iurretame32D/CO2-out/4.taldea/3D Kutxa/Erabilitako Linkak/linkak.odt

DHT_11

https://randomnerdtutorials.com/esp32-dht11-dht22-temperature-humidity-sensor-arduino-ide/

HEAT INDEX (sentsazio termikoa)

The heat index is a parameter that takes into account temperature and relative humidity, to determine the apparent temperature or the human perceived equivalent temperature.

Liburutegia eta kontrol aukerak

https://github.com/mysensors/MySensorsArduinoExamples/pull/35/files

CCS811

https://www.luisllamas.es/medir-calidad-del-aire-y-co2-con-ccs811-y-arduino/

LoRa

https://www.iagua.es/blogs/carles-bianciotto/conectar-sensor-lorawan-cero

https://bricolabs.cc/wiki/guias/lora_ttn

PINOUT erabilita daudenak eta liburutegiak

https://randomnerdtutorials.com/ttgo-lora32-sx1276-arduino-ide/

IKUSTEKO TTN pausuak

https://akirasan.net/nodo-lorawan-con-esp32/
