iurretame32D/CO2-out/Ataldea/Txostena/ZATIKA/Bloke_Diagrama.odt

# Bloke-diagramak

Lehen bertsioa izango da hau. Erronkaren amaieran igo egingo duzue azken bertsioa.

## Softwarearen hasierako bloke-diagrama

Softwarea: geziekin, bloke bakoitza zelan eta zertarako erabiliko den azalduta azpian. Aldagaiak eta funtzioen izenak aurreikustea ere komeniko litzateke. Sekuentzia edo ordena inportantea dela kontutan izan.

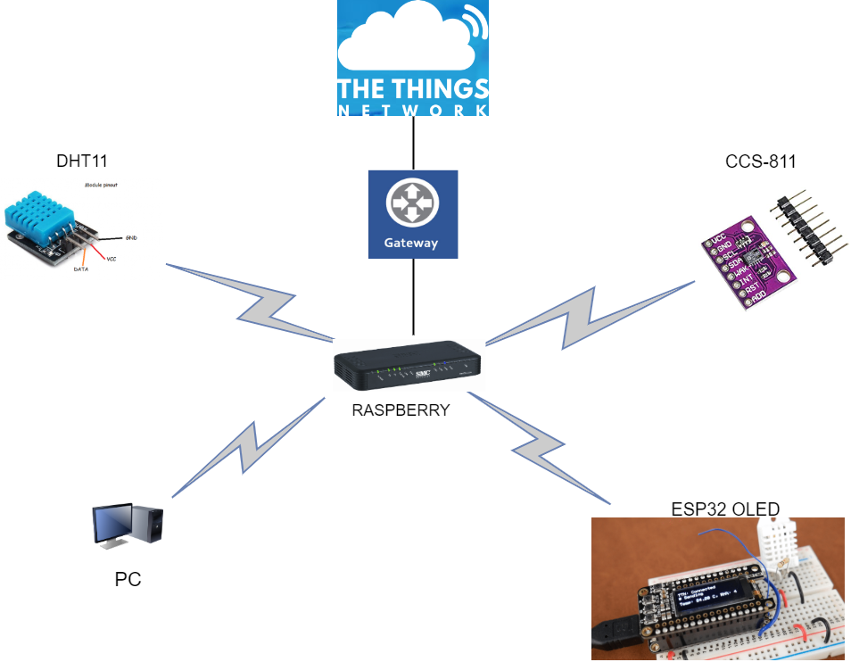
[picture p149: figure]

## Hardwarearen hasierako bloke-diagram

Hardwarea: geziekin, bloke bakoitza zelan eta zertarako erabiliko den azalduta azpian.

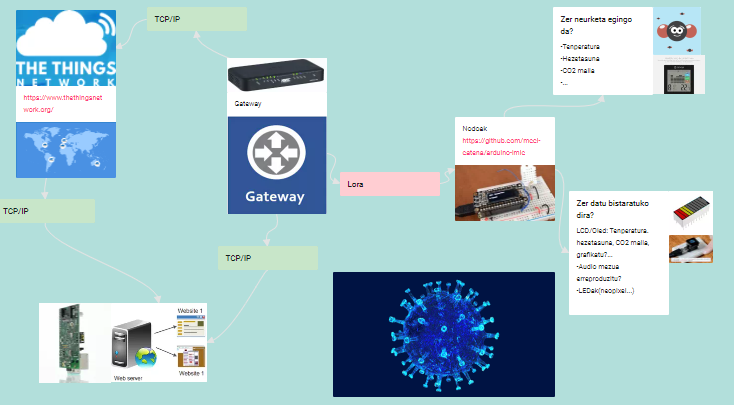
[picture p150: figure]

## Softwarearen amaierako bloke-diagrama

Softwarea: geziekin, bloke bakoitza zelan eta zertarako erabiliko den azalduta azpian. Aldagaiak eta funtzioen izenak aurreikustea ere komeniko litzateke. Sekuentzia edo ordena inportantea dela kontutan izan.

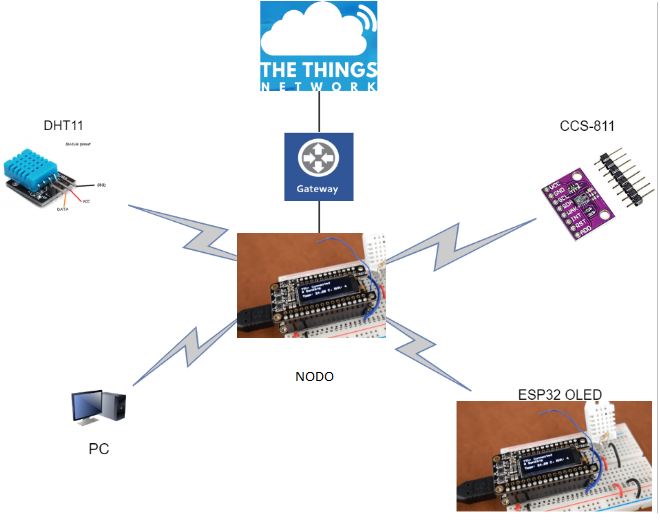
[picture p151: figure]

## Hardwarearen amaierako bloke-diagrama

Hardwarea: geziekin, bloke bakoitza zelan eta zertarako erabiliko den azalduta azpian.

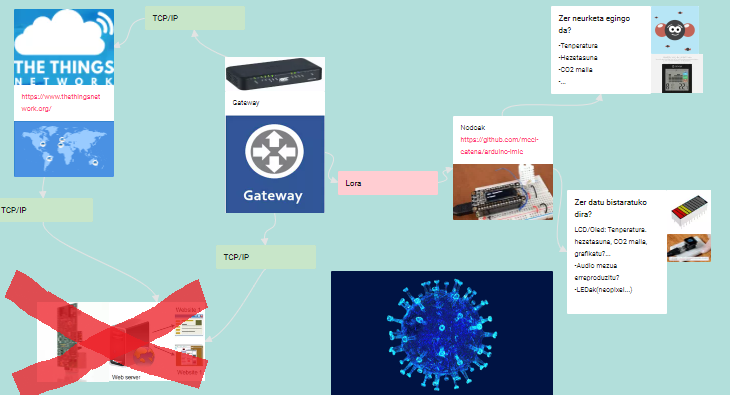
[picture p152: figure]
