iurretame32D/CO2-out/Talde3AnderBJonS/Txostenak/Atalak/BlokeDiagramak.odt

# Bloke-diagramak

## Softwarearen hasierako bloke-diagrama

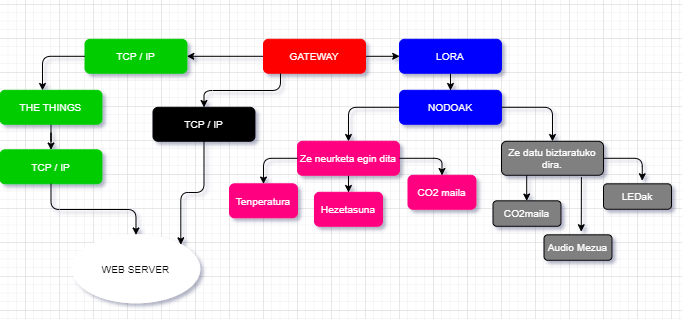
[picture p153: figure]

## Hardwarearen hasierako bloke-diagrama

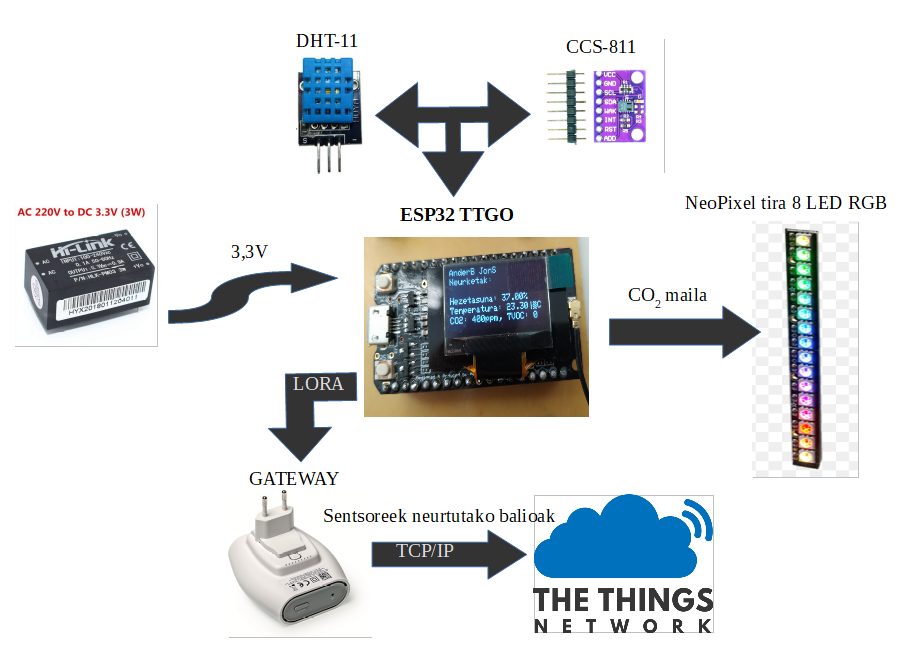
[picture p154: figure]
