iurretame32D/CO2-out/Talde3AnderBJonS/Txostenak/Atalak/ErronkarenPlanteamendua.odt

# Erronkaren planteamendua

Erronka honetan bi sentsore erabiliko ditugu, DHT-11 hezetasun eta tenperatura sentsorea eta CJMU-811 edo CCS-811 aireko CO2 kantitatea eta TVOC (bolatil konposatu organikoak) neurtze duena.

ESP32 TTGO kontrolagailuarekin lan egingo dugu, eta LORA komunikazioa erabiliko dugu, gure kontrolagailua, konfiguratu dugun GateWay-arekin komunikatzeko eta balioak partekatu ahal izateko.

Ondoren GateWay-a konfiguratu dugu TTN (The things Network)ean sortu dugun kontu batean sentsoreetako balioak bertan bistaratzeko.

Eta azkenik Raspberry bat erabiliz dashboard edo aginte panel bat sortzeko eta hor partekatzeko gure ditugun balioak edo informazioa.

Gure helburua elektronika eraikinaren geletako CO2 kantiatea, tenperatura eta hezetasunaren kontrola izatea da, eta edozein lekutan egonda, balio hauek ikus ahal izatea.

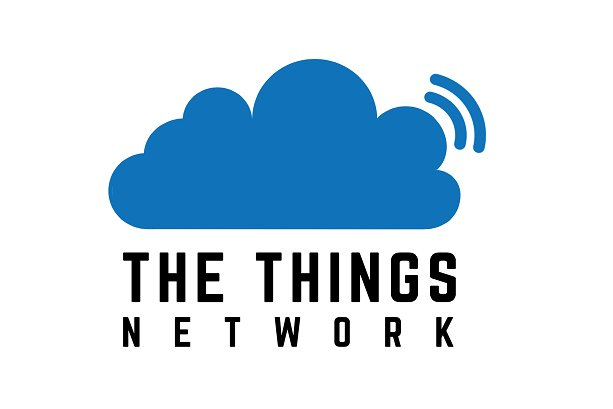
[picture p155: figure]
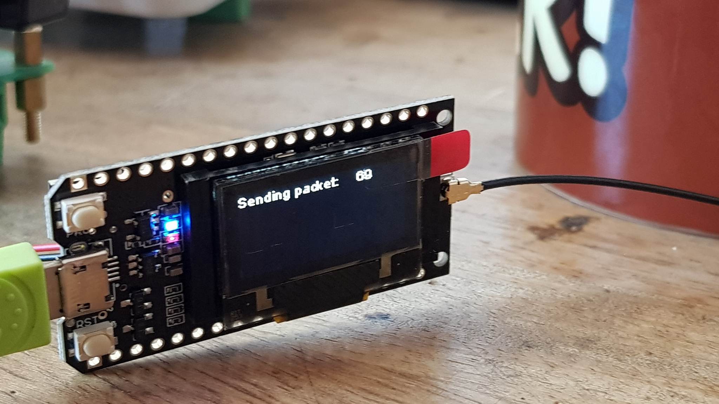
[picture p156: figure]
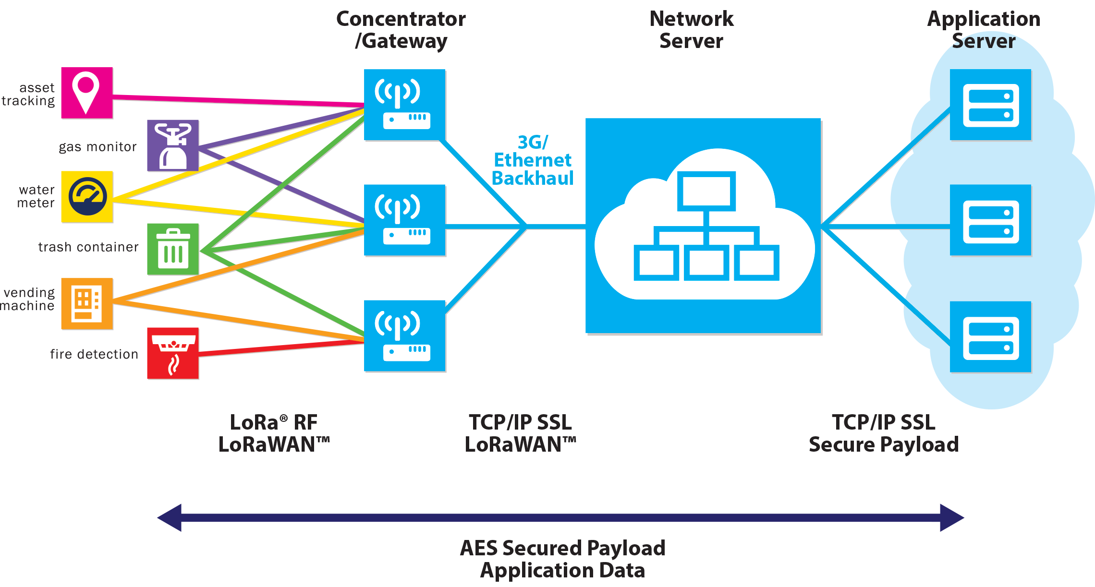
[picture p157: figure]
