iurretame32D/CO2-out/Talde3AnderBJonS/FRITZING/ccs811-arduino-1200x690.jpg

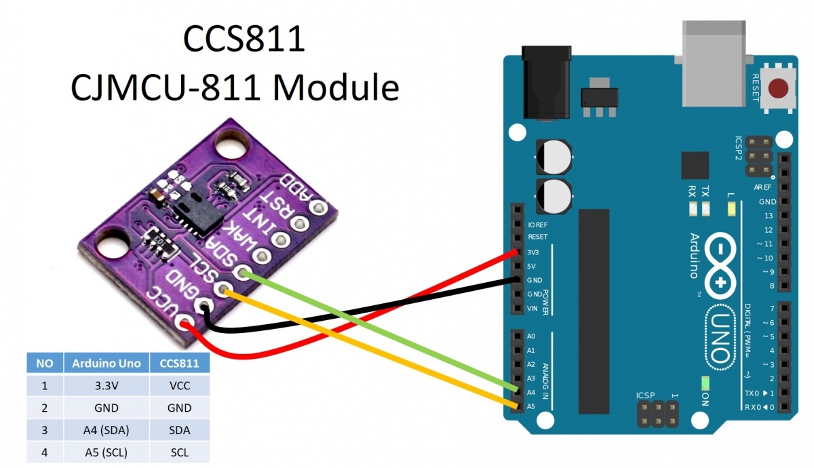
Talde3AnderBJonS/FRITZING/ccs811-arduino-1200x690.jpg
