iurretame32D/CO2-out/Talde3AnderBJonS/FRITZING/CCS811/CCS811_bb.png

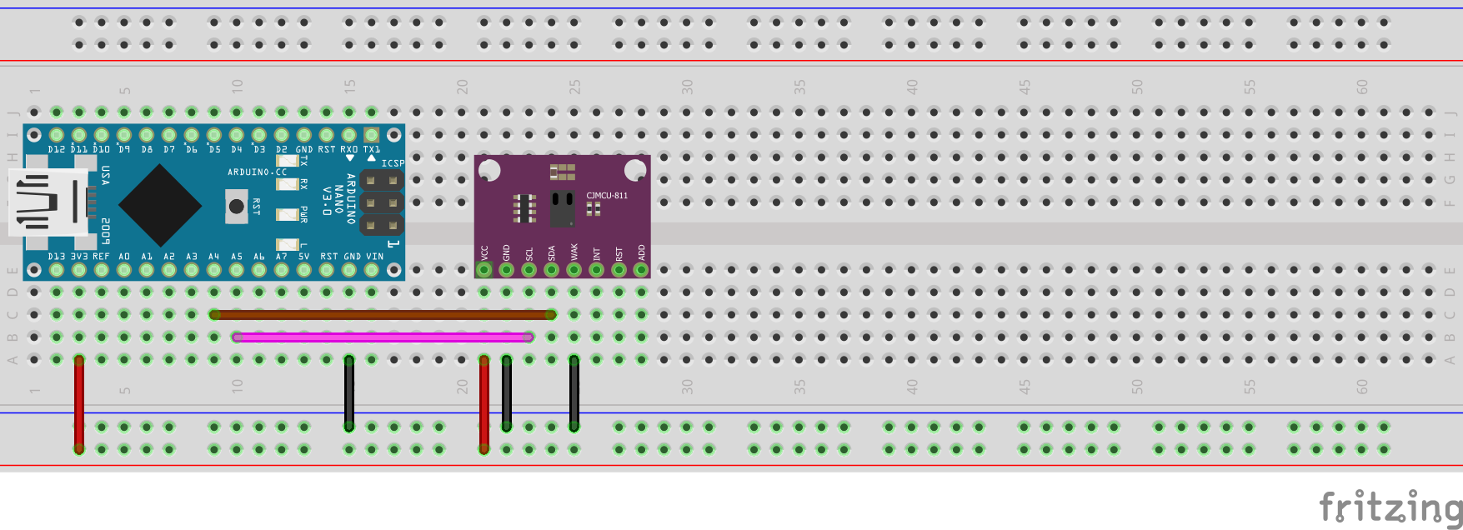
Talde3AnderBJonS/FRITZING/CCS811/CCS811_bb.png
