iurretame32D/CO2-out/Talde3AnderBJonS/FRITZING/cjmcu-811.png

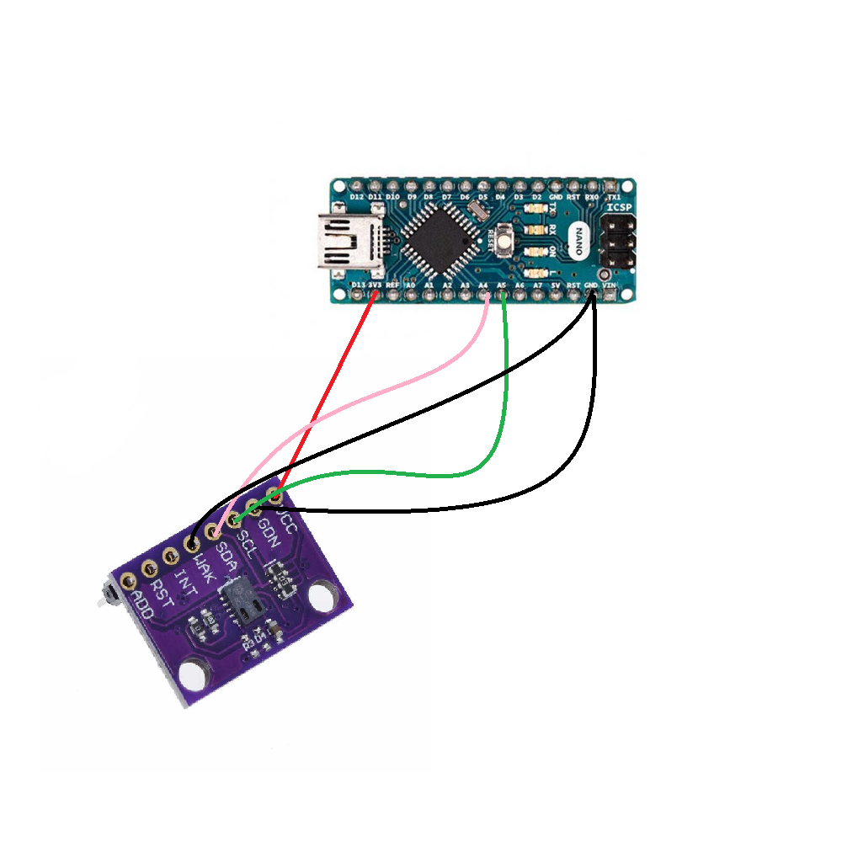
Talde3AnderBJonS/FRITZING/cjmcu-811.png
