iurretame32D/CO2-out/Talde3AnderBJonS/FRITZING/DHT11/DHT11.PNG

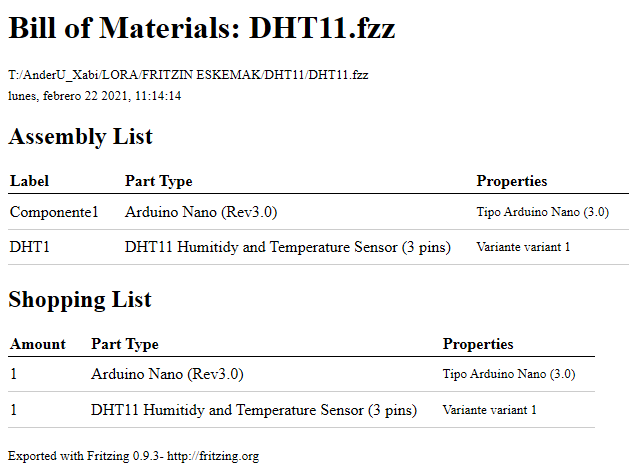
Talde3AnderBJonS/FRITZING/DHT11/DHT11.PNG
