iurretame32D/CO2-out/2.taldea/Proiektu Finala 2.Taldea/Arduino Programa/TTN_komunikazioa_proba/TTN_komunikazioa_proba.ino

#include <TheThingsNetwork.h>

// First install "DHT sensor library" via the Library Manager
#include <DHT.h>

// Set your AppEUI and AppKey
const char *appEui = "0000000000000000";
const char *appKey = "00000000000000000000000000000000";

#define loraSerial Serial1
#define debugSerial Serial

// Replace REPLACE_ME with TTN_FP_EU868 or TTN_FP_US915
#define freqPlan TTN_FP_EU868

#define DHTPIN 17

//Choose your DHT sensor moddel
#define DHTTYPE DHT11
//#define DHTTYPE DHT21
//#define DHTTYPE DHT22

DHT dht(DHTPIN, DHTTYPE);

TheThingsNetwork ttn(loraSerial, debugSerial, freqPlan);

void setup()
{
  loraSerial.begin(57600);
  debugSerial.begin(9600);

  // Wait a maximum of 10s for Serial Monitor
  while (!debugSerial && millis() < 10000)
    ;

  debugSerial.println("-- STATUS");
  ttn.showStatus();

  debugSerial.println("-- JOIN");
  ttn.join(appEui, appKey);

  dht.begin();
}

void loop()
{
  debugSerial.println("-- LOOP");

  // Read sensor values and multiply by 100 to effictively have 2 decimals
  uint16_t humidity = dht.readHumidity(false) * 100;

  // false: Celsius (default)
  // true: Farenheit
  uint16_t temperature = dht.readTemperature(false) * 100;

  // Split both words (16 bits) into 2 bytes of 8
  byte payload[4];
  payload[0] = highByte(temperature);
  payload[1] = lowByte(temperature);
  payload[2] = highByte(humidity);
  payload[3] = lowByte(humidity);

  debugSerial.print("Temperature: ");
  debugSerial.println(temperature);
  debugSerial.print("Humidity: ");
  debugSerial.println(humidity);

  ttn.sendBytes(payload, sizeof(payload));

  delay(20000);
}
