iurretame32D/CO2-out/2.taldea/Proiektu Finala 2.Taldea/Arduino Programa/Oled_proba/modified_font.h

// Created by http://oleddisplay.squix.ch/ Consider a donation
// In case of problems make sure that you are using the font file with the correct version!
const char Open_Sans_Condensed_Light_20[] PROGMEM = {
  0x11, // Width: 17
  0x1C, // Height: 28
  0x20, // First Char: 32
  0xE0, // Numbers of Chars: 224

  // Jump Table:
  0xFF, 0xFF, 0x00, 0x04,  // 32:65535
  0x00, 0x00, 0x07, 0x03,  // 33:0
  0x00, 0x07, 0x12, 0x06,  // 34:7
  0x00, 0x19, 0x1F, 0x08,  // 35:25
  0x00, 0x38, 0x17, 0x07,  // 36:56
  0x00, 0x4F, 0x2B, 0x0C,  // 37:79
  0x00, 0x7A, 0x1F, 0x09,  // 38:122
  0x00, 0x99, 0x06, 0x03,  // 39:153
  0x00, 0x9F, 0x10, 0x05,  // 40:159
  0x00, 0xAF, 0x0F, 0x05,  // 41:175
  0x00, 0xBE, 0x16, 0x07,  // 42:190
  0x00, 0xD4, 0x1E, 0x09,  // 43:212
  0x00, 0xF2, 0x0B, 0x04,  // 44:242
  0x00, 0xFD, 0x13, 0x06,  // 45:253
  0x01, 0x10, 0x07, 0x03,  // 46:272
  0x01, 0x17, 0x16, 0x07,  // 47:279
  0x01, 0x2D, 0x1B, 0x08,  // 48:301
  0x01, 0x48, 0x13, 0x08,  // 49:328
  0x01, 0x5B, 0x1B, 0x08,  // 50:347
  0x01, 0x76, 0x1B, 0x08,  // 51:374
  0x01, 0x91, 0x23, 0x09,  // 52:401
  0x01, 0xB4, 0x1B, 0x08,  // 53:436
  0x01, 0xCF, 0x1B, 0x08,  // 54:463
  0x01, 0xEA, 0x1A, 0x08,  // 55:490
  0x02, 0x04, 0x1F, 0x09,  // 56:516
  0x02, 0x23, 0x1B, 0x08,  // 57:547
  0x02, 0x3E, 0x07, 0x03,  // 58:574
  0x02, 0x45, 0x07, 0x03,  // 59:581
  0x02, 0x4C, 0x1F, 0x09,  // 60:588
  0x02, 0x6B, 0x1B, 0x08,  // 61:619
  0x02, 0x86, 0x1E, 0x09,  // 62:646
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
  0x00,0x00,0x00,0x00,0x00,0x00,0x00,0x00,0x80,0xFF,0x3F,0x00,0x00,0x40,0x00,0x00,0x00,0x40,0x00,0x00,0x00,0x40,0x00,0x00,0x00,0x40,0x00,0x00,0x00,0x40,0x00,0x00,0x80,0xFF,0x3F, // 72
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
